mariusgerdes/hybrid-electrode/3d-models/electrode.png

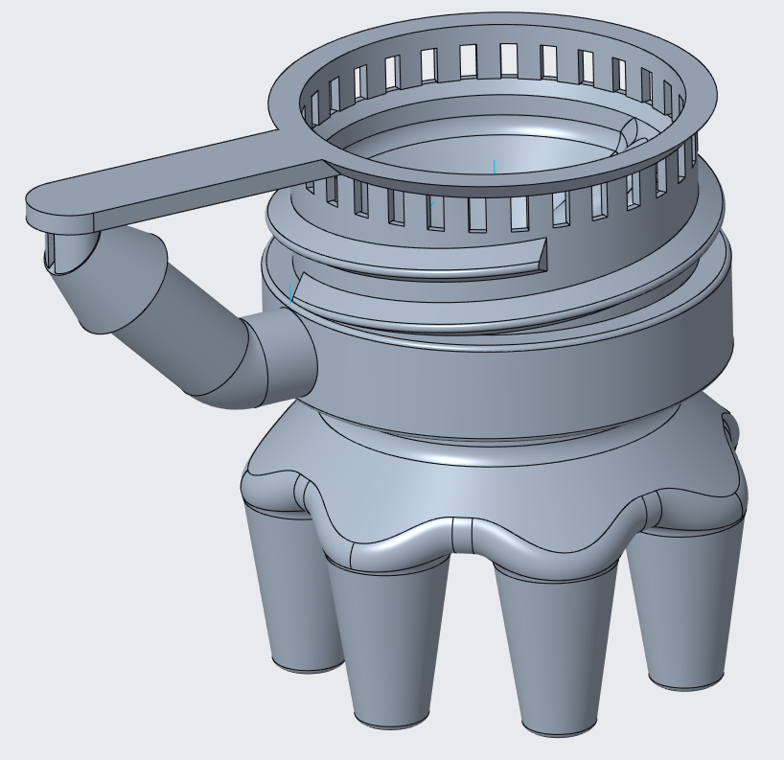
3d-models/electrode.png
