mariusgerdes/hybrid-electrode/plots/Electrode_Comparison.png

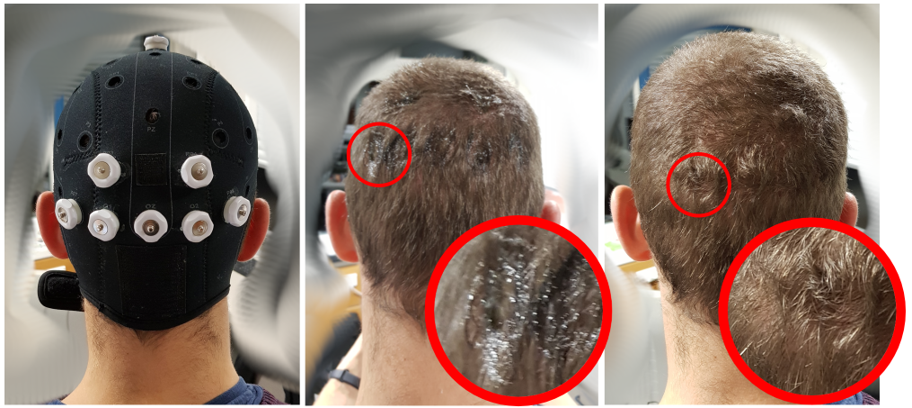
plots/Electrode_Comparison.png
