mariusgerdes/hybrid-electrode/plots/filling.png

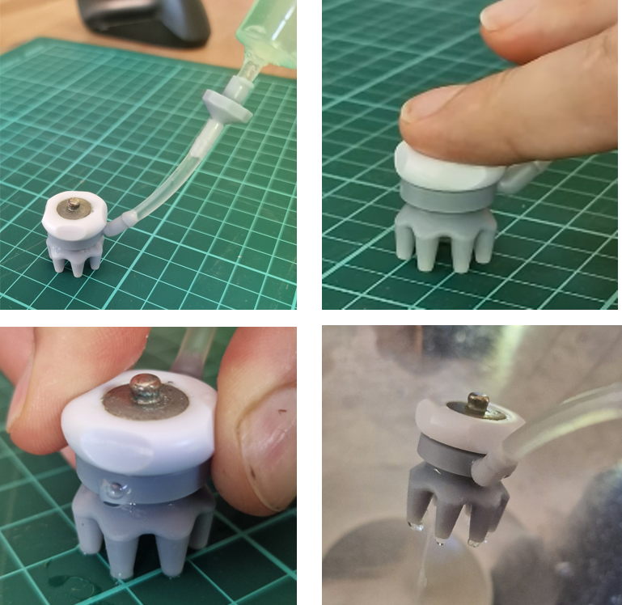
plots/filling.png
