mariusgerdes/hybrid-electrode/video_and_photo/filling_utensils.jpg

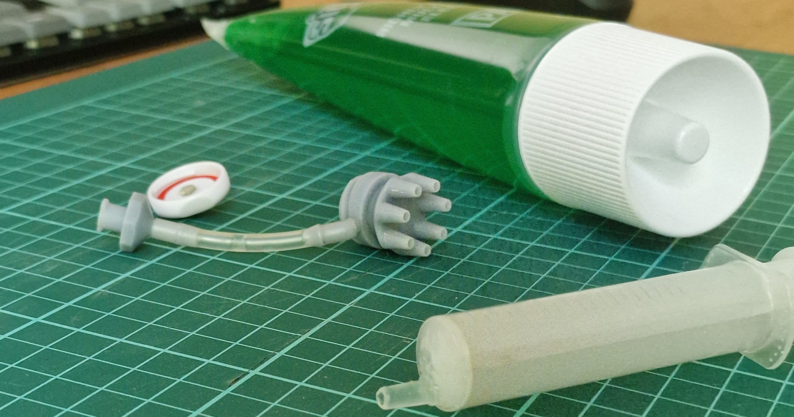
video_and_photo/filling_utensils.jpg
